darknecrocities/EasyLense-Frame-3dBlueprint/version3/left_temple.stl

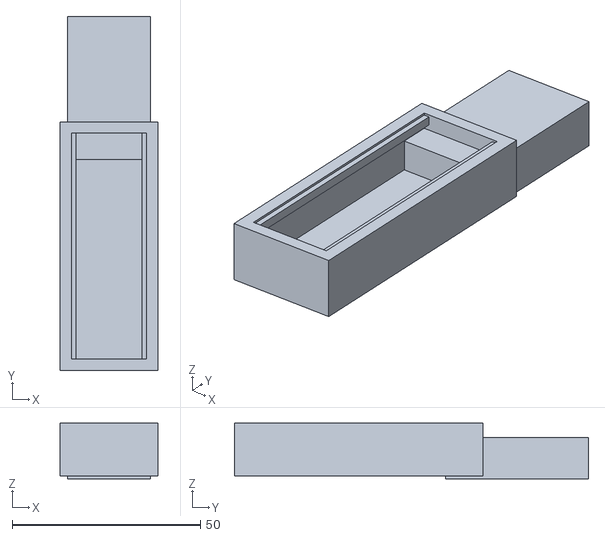
[picture p15: CAD file, 2026-06-14, an earlier design]
version3/left_temple.stl
26.0 x 94.0 x 14.8
